yths42/Sandwich-machine/Pictures of machine/IMG_8090 Large.jpeg

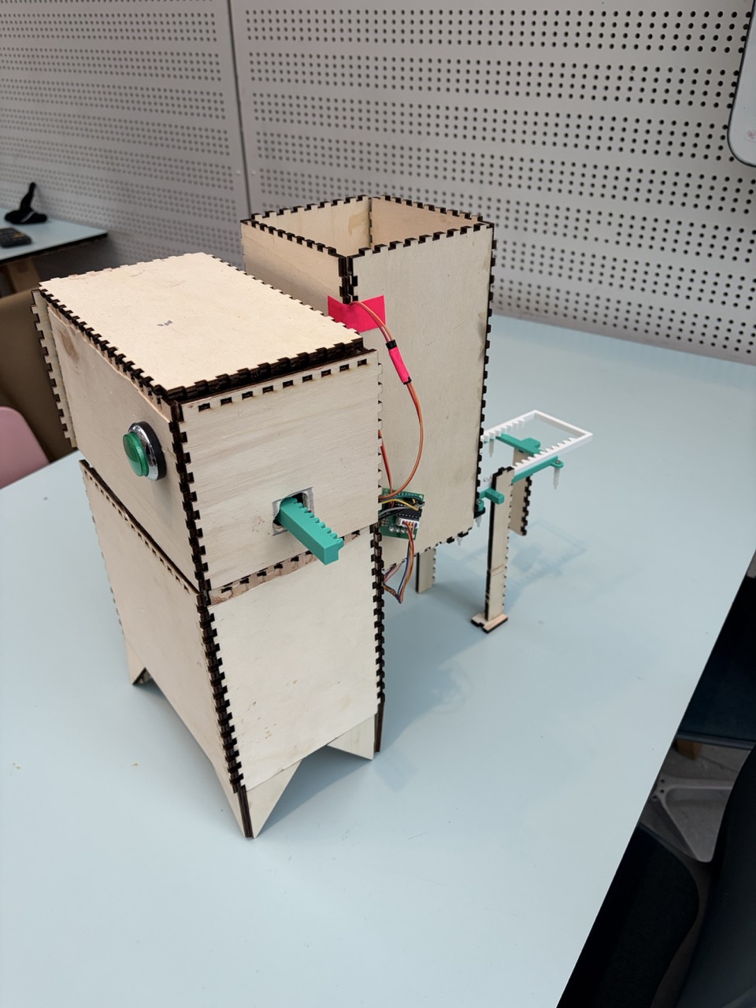
Pictures of machine/IMG_8090 Large.jpeg
