yths42/Sandwich-machine/Pictures of machine/IMG_8092 Large.jpeg

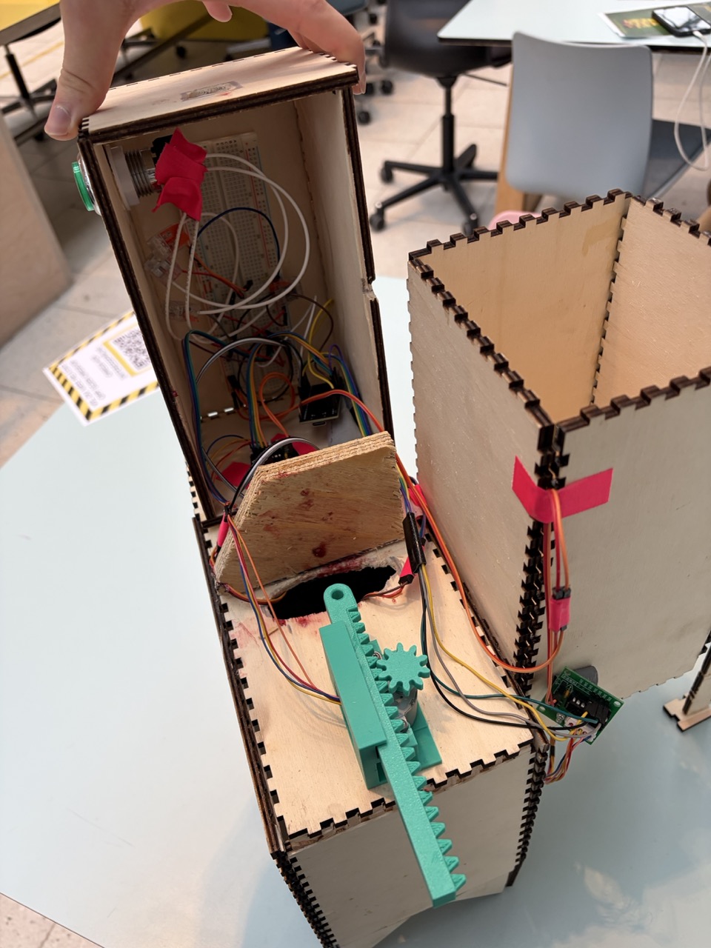
Pictures of machine/IMG_8092 Large.jpeg
